dromer/2026DutchHackerspaceMap/Hardware/hackerspacemap.kicad_sch

## KiCad design Hardware/hackerspacemap.kicad_sch (2026-04-04)

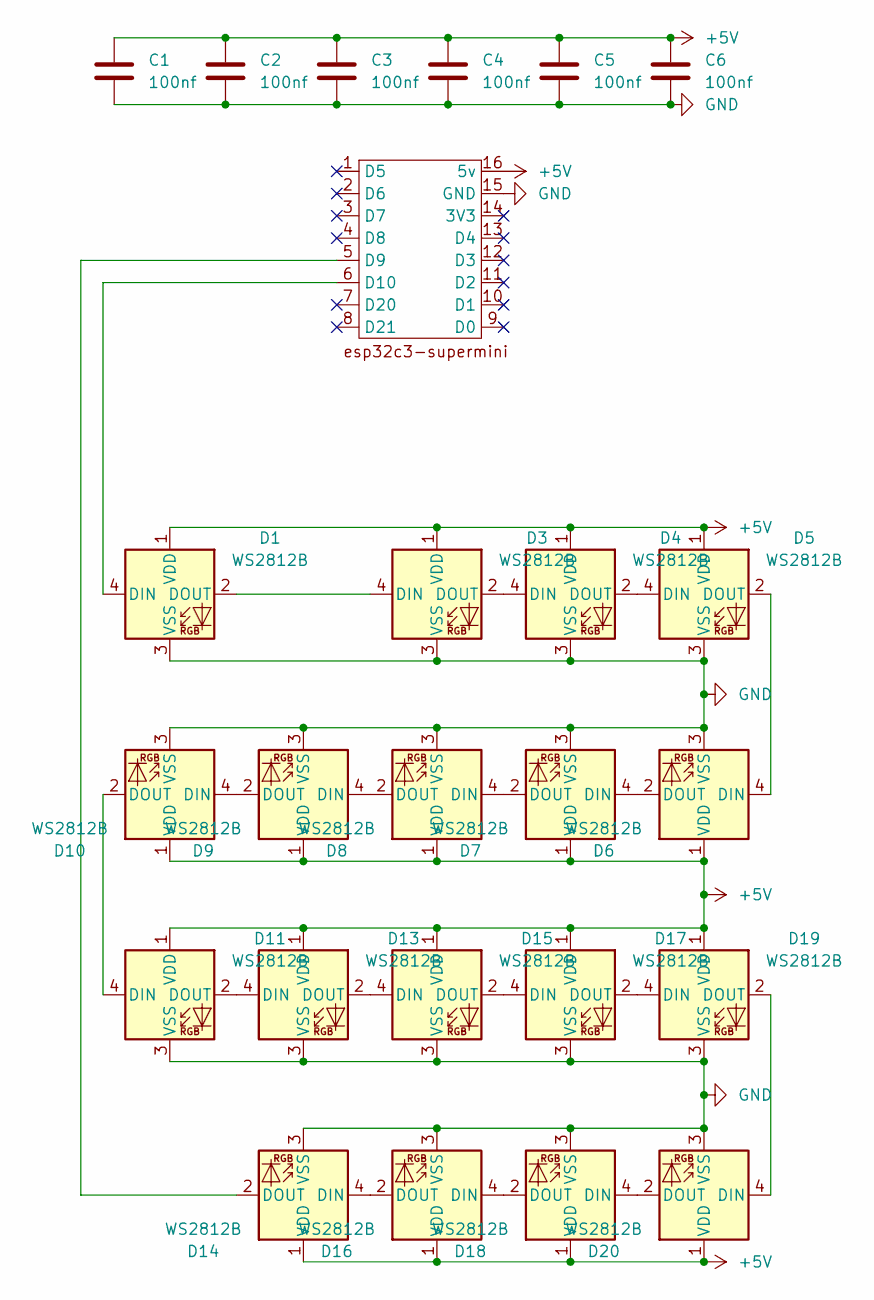
[picture p2: schematic hackerspacemap.kicad_sch]

Parts:
C1, C2, C3, C4, C5, C6: 100nf; C_0805_2012Metric_Pad1.18x1.45mm_HandSolder
D1, D3, D4, D5, D6, D7, D8, D9, D10, D11, D14, D16, D17, D19: WS2812B; XINGLIGHT XL-0807RGBC-WS2812B-S
D13, D20: WS2812B; XINGLIGHT XL-0807RGBC-WS2812B-S_C_variant
D15, D18: WS2812B; XINGLIGHT XL-0807RGBC-WS2812B-S_B_variant
U1: esp32c3

Connections:
+5V: C1.1, C2.1, C3.1, C4.1, C5.1, C6.1, D1.1 (VDD), D3.1 (VDD), D4.1 (VDD), D5.1 (VDD), D6.1 (VDD), D7.1 (VDD), D8.1 (VDD), D9.1 (VDD), D10.1 (VDD), D11.1 (VDD), D13.1 (VDD), D14.1 (VDD), D15.1 (VDD), D16.1 (VDD), D17.1 (VDD), D18.1 (VDD), D19.1 (VDD), D20.1 (VDD), U1.16 (5v)
GND: C1.2, C2.2, C3.2, C4.2, C5.2, C6.2, D1.3 (VSS), D3.3 (VSS), D4.3 (VSS), D5.3 (VSS), D6.3 (VSS), D7.3 (VSS), D8.3 (VSS), D9.3 (VSS), D10.3 (VSS), D11.3 (VSS), D13.3 (VSS), D14.3 (VSS), D15.3 (VSS), D16.3 (VSS), D17.3 (VSS), D18.3 (VSS), D19.3 (VSS), D20.3 (VSS), U1.15 (GND)
unnamed: D1.2 (DOUT), D3.4 (DIN)
unnamed: D1.4 (DIN), U1.6 (D10)
unnamed: D3.2 (DOUT), D4.4 (DIN)
unnamed: D4.2 (DOUT), D5.4 (DIN)
unnamed: D5.2 (DOUT), D6.4 (DIN)
unnamed: D6.2 (DOUT), D7.4 (DIN)
unnamed: D7.2 (DOUT), D8.4 (DIN)
unnamed: D8.2 (DOUT), D9.4 (DIN)
unnamed: D10.2 (DOUT), D11.4 (DIN)
unnamed: D9.2 (DOUT), D10.4 (DIN)
unnamed: D11.2 (DOUT), D13.4 (DIN)
unnamed: D13.2 (DOUT), D15.4 (DIN)
unnamed: D14.2 (DOUT), U1.5 (D9)
unnamed: D14.4 (DIN), D16.2 (DOUT)
unnamed: D15.2 (DOUT), D17.4 (DIN)
unnamed: D16.4 (DIN), D18.2 (DOUT)
unnamed: D17.2 (DOUT), D19.4 (DIN)
unnamed: D18.4 (DIN), D20.2 (DOUT)
unnamed: D19.2 (DOUT), D20.4 (DIN)
